embed-me/knx-kmp-watermeter/firmware/src/drivers/IDriverFactory.hpp

#ifndef _I_DRIVER_FACTORY_HPP_
#define _I_DRIVER_FACTORY_HPP_

#include "ITimerDriverFactory.hpp"
#include "IGpioDriverFactory.hpp"
#include "IKnxDriverFactory.hpp"
#include "IMotionDriverFactory.hpp"
#include "IWatermeterWakeupDriverFactory.hpp"
#include "rtc/IRtcDriver.hpp"
#include "logger/ILogger.hpp"
#include "watchdog/IWatchdogDriver.hpp"
#include "uart/IUartDriver.hpp"

namespace drivers {

class IDriverFactory : public IGpioDriverFactory,
                       public IKnxDriverFactory,
                       public IMotionDriverFactory,
                       public IWatermeterWakeupDriverFactory
{
public:
    ~IDriverFactory() = default;

    virtual std::shared_ptr<logger::ILogger> getLoggerDriver() = 0;
    virtual std::shared_ptr<watchdog::IWatchdogDriver> getWatchdogDriver() = 0;
    virtual std::shared_ptr<uart::IUartDriver> getUartDriver() = 0;
    virtual std::shared_ptr<timer::ITimerDriverFactory> getTimerDriverFactory() = 0;
    virtual std::shared_ptr<rtc::IRtcDriver> getRtcDriver() = 0;
};

}

#endif //_I_DRIVER_FACTORY_HPP_
