embed-me/knx-kmp-watermeter/firmware/src/application/WatermeterApp.cpp

#include "WatermeterApp.hpp"
#include "../drivers/logger/Logger.hpp"
#include "../utils/scheduler/Scheduler.hpp"
#include "../utils/knx/KnxDateTimeParser.hpp"
#include "../utils/knx/RtcSyncState.hpp"

using namespace drivers::logger;

constexpr uint32_t USEC_PER_SEC = 1000000;
constexpr uint32_t CRON_TICK_INTERVAL_US = 60 * USEC_PER_SEC;

namespace kmp = drivers::watermeter::kamstrup::transport;

namespace application {

WatermeterApp::WatermeterApp()
    : queueConfig_{}
{
}

void WatermeterApp::init(
    std::shared_ptr<drivers::uart::IUartDriver> uart,
    const drivers::uart::UartConfig& uartConfig,
    drivers::knx::KnxConfig& knxConfig,
    const kmp::CommandQueueConfig& queueConfig,
    std::shared_ptr<drivers::watermeter::wakeup::IWatermeterWakeupDriver> wakeupDriver,
    std::shared_ptr<drivers::timer::ITimerDriverFactory> timerFactory,
    std::shared_ptr<drivers::rtc::IRtcDriver> rtcDriver)
{
    knxConfig_ = &knxConfig;
    queueConfig_ = queueConfig;
    wakeupDriver_ = wakeupDriver;
    rtcDriver_ = rtcDriver;
    kmpUart_ = uart;
    if (!kmpUart_) {
        logWarning("KMP UART driver not available");
        return;
    }

    if (!kmpUart_->init(uartConfig)) {
        logError("KMP UART initialization failed");
        return;
    }

    initTransport(kmpUart_);
    if (kmpApplication_) {
        initRegisterCommands();
        initQueue(timerFactory);
        initTimers(timerFactory);
        initRtcCron();
    }
}

void WatermeterApp::process()
{
    if (kmpUart_) {
        kmpUart_->process();
    }
}

void WatermeterApp::initTransport(std::shared_ptr<drivers::uart::IUartDriver> uart)
{
    uint8_t addr = knxConfig_->getWatermeterConfig().destinationAddress;
    kmpPhysical_ = std::make_shared<kmp::PhysicalLayer>(uart);
    kmpDataLink_ = std::make_shared<kmp::DataLinkLayer>(kmpPhysical_, addr);
    kmpApplication_ = std::make_shared<kmp::ApplicationLayer>(kmpDataLink_);
    logInfo("KMP transport stack initialized");
}

void WatermeterApp::initRegisterCommands()
{
    auto regCfgs = knxConfig_->getWatermeterRegisterConfigs();
    auto linked = knxConfig_->getLinkedState();

    for (auto& reg : regCfgs) {
        if (!reg.enabled) {
            continue;
        }

        auto cmd = std::make_shared<kmp::GetRegisterCommand>(kmpApplication_, reg.registerId);
        cmd->registerListener([name = reg.name, go = reg.groupObject, dpt = reg.dpt,
                               linkGo = linked.groupObject, linkDpt = linked.dpt](const kmp::CommandResult& res){
            bool isOk = res.result == kmp::CommandResult::Result::OK;
            if (linkGo) {
                linkGo->valueCompare(KNXValue(isOk), linkDpt);
            }
            if (go && isOk) {
                go->value(KNXValue(res.value), dpt);
                logInfo("%s: %g %s", name, res.value,
                        kmp::unitToString(res.unit).c_str());
            } else {
                logWarning("Failed to get %s: with error %d", name, res.result);
            }
        });
        registerCmds_.push_back(cmd);
    }
}

void WatermeterApp::initQueue(std::shared_ptr<drivers::timer::ITimerDriverFactory> timerFactory)
{
    commandQueue_ = std::make_shared<kmp::CommandQueue>(
        kmpApplication_, queueConfig_, timerFactory);

    commandQueue_->setOnEmpty([this]() {
        onQueueEmpty();
    });
}

void WatermeterApp::initTimers(std::shared_ptr<drivers::timer::ITimerDriverFactory> timerFactory)
{
    cronTickTimer_ = timerFactory->getTimer();
    cronTickTimer_->setupInterruptHandler([](void* arg){
        auto* self = static_cast<WatermeterApp*>(arg);
        utils::Scheduler::schedule([self](void*) {
            self->onCronTick();
        });
    }, this);

    cronTickTimer_->start(CRON_TICK_INTERVAL_US, drivers::timer::TimerMode::RECURRING);
}

void WatermeterApp::initRtcCron()
{
    auto& timeGo = knxConfig_->getTimeGroupObject();
    timeGo.callback([this](GroupObject& go) {
        auto t = utils::knx::parseKnxTime(go.valueRef(), go.valueSize());
        if (!t.valid) {
            logWarning("Invalid KNX time telegram ignored");
            return;
        }

        if (rtcSync_.updateTime(t) && rtcDriver_) {
            const auto& dt = rtcSync_.dateTime();
            rtcDriver_->setDateTime(dt);
            logInfo("RTC updated from KNX: %04d-%02d-%02d %02d:%02d:%02d",
                    dt.year, dt.month, dt.day,
                    dt.hour, dt.minute, dt.second);
        }
    });

    auto& dateGo = knxConfig_->getDateGroupObject();
    dateGo.callback([this](GroupObject& go) {
        auto d = utils::knx::parseKnxDate(go.valueRef(), go.valueSize());
        if (!d.valid) {
            logWarning("Invalid KNX date telegram ignored");
            return;
        }

        if (rtcSync_.updateDate(d) && rtcDriver_) {
            const auto& dt = rtcSync_.dateTime();
            rtcDriver_->setDateTime(dt);
            logInfo("RTC updated from KNX: %04d-%02d-%02d %02d:%02d:%02d",
                    dt.year, dt.month, dt.day,
                    dt.hour, dt.minute, dt.second);
        }
    });

    updateCronMatcher();
}

void WatermeterApp::enqueuePendingCommands()
{
    if (commandQueue_) {
        for (auto& cmd : registerCmds_) {
            if (cmd) {
                commandQueue_->enqueue(cmd);
            }
        }
    }
}

void WatermeterApp::onQueueEmpty()
{
    wakeupDriver_->sleep();
}

void WatermeterApp::onCronTick()
{
    updateCronMatcher();

    if (!cronMatcher_ || !rtcDriver_) {
        return;
    }

    auto now = rtcDriver_->getDateTime();

    if (cronMatcher_->matches(now)) {
        int currentMinute = now.hour * 60 + now.minute;
        if (currentMinute != lastPollMinute_) {
            lastPollMinute_ = currentMinute;
            triggerDataRead();
        }
    }
}

void WatermeterApp::updateCronMatcher()
{
    if (!knxConfig_) return;

    auto cronExpr = knxConfig_->getPollingCronExpression();
    if (cronExpr == lastCronExpression_) {
        return;
    }

    lastCronExpression_ = cronExpr;
    if (cronExpr.empty()) {
        cronMatcher_.reset();
        logWarning("Cron expression is empty, data polling disabled");
        return;
    }

    cronMatcher_ = std::make_unique<utils::cron::CronMatcher>(cronExpr);
    logInfo("Cron expression updated: %s", cronExpr.c_str());
}

void WatermeterApp::triggerDataRead()
{
    wakeupDriver_->wakeup([this]() {
        enqueuePendingCommands();
    });
}

} // namespace application
