embed-me/knx-kmp-watermeter/firmware/src/application/WatermeterApp.hpp

#ifndef _WATERMETER_APP_HPP_
#define _WATERMETER_APP_HPP_

#include "IApplication.hpp"
#include "../drivers/watermeter/kamstrup/transport/layers/physical/PhysicalLayer.hpp"
#include "../drivers/watermeter/kamstrup/transport/layers/data_link/DataLinkLayer.hpp"
#include "../drivers/watermeter/kamstrup/transport/layers/application/ApplicationLayer.hpp"
#include "../drivers/watermeter/kamstrup/commands/GetRegisterCommand.hpp"
#include "../drivers/watermeter/kamstrup/utils/CommandQueue.hpp"
#include "../drivers/watermeter/wakeup/IWatermeterWakeupDriver.hpp"

#include "../drivers/rtc/IRtcDriver.hpp"
#include "../drivers/timer/ArduinoTimerFactory.hpp"
#include "../drivers/timer/ITimer.hpp"
#include "../utils/cron/CronMatcher.hpp"
#include "../utils/knx/RtcSyncState.hpp"

#include <memory>
#include <cstdint>
#include <vector>
#include <string>

namespace application {

class WatermeterApp : public IApplication {
public:
    WatermeterApp();
    ~WatermeterApp() override = default;

    void init(
        std::shared_ptr<drivers::uart::IUartDriver> uart,
        const drivers::uart::UartConfig& uartConfig,
        drivers::knx::KnxConfig& knxConfig,
        const drivers::watermeter::kamstrup::transport::CommandQueueConfig& queueConfig,
        std::shared_ptr<drivers::watermeter::wakeup::IWatermeterWakeupDriver> wakeupDriver,
        std::shared_ptr<drivers::timer::ITimerDriverFactory> timerFactory,
        std::shared_ptr<drivers::rtc::IRtcDriver> rtcDriver
    );
    void process() override;

private:
    void initTransport(std::shared_ptr<drivers::uart::IUartDriver> uart);
    void initRegisterCommands();
    void initQueue(std::shared_ptr<drivers::timer::ITimerDriverFactory> timerFactory);
    void initTimers(std::shared_ptr<drivers::timer::ITimerDriverFactory> timerFactory);
    void initRtcCron();
    void enqueuePendingCommands();
    void onQueueEmpty();

    void onCronTick();
    void updateCronMatcher();
    void triggerDataRead();

    std::shared_ptr<drivers::watermeter::kamstrup::transport::IPhysicalLayer> kmpPhysical_;
    std::shared_ptr<drivers::watermeter::kamstrup::transport::IDataLinkLayer> kmpDataLink_;
    std::shared_ptr<drivers::watermeter::kamstrup::transport::IApplicationLayer> kmpApplication_;

    std::vector<std::shared_ptr<drivers::watermeter::kamstrup::transport::GetRegisterCommand>> registerCmds_;

    std::shared_ptr<drivers::watermeter::kamstrup::transport::CommandQueue> commandQueue_;
    std::shared_ptr<drivers::timer::ITimer> cronTickTimer_;

    std::shared_ptr<drivers::uart::IUartDriver> kmpUart_;
    drivers::knx::KnxConfig* knxConfig_ = nullptr;
    drivers::watermeter::kamstrup::transport::CommandQueueConfig queueConfig_;

    std::shared_ptr<drivers::watermeter::wakeup::IWatermeterWakeupDriver> wakeupDriver_;

    std::shared_ptr<drivers::rtc::IRtcDriver> rtcDriver_;
    std::unique_ptr<utils::cron::CronMatcher> cronMatcher_;
    std::string lastCronExpression_;
    int lastPollMinute_ = -1;
    utils::knx::RtcSyncState rtcSync_;
};

}

#endif // _WATERMETER_APP_HPP_
