embed-me/knx-kmp-watermeter/firmware/src/application/IApplication.hpp

#ifndef _I_APPLICATION_HPP_
#define _I_APPLICATION_HPP_

#include "../drivers/uart/IUartDriver.hpp"
#include "../drivers/timer/ArduinoTimerFactory.hpp"
#include "../drivers/knx/data/KnxConfig.hpp"
#include "../drivers/rtc/IRtcDriver.hpp"
#include "../drivers/watermeter/kamstrup/utils/CommandQueueConfig.hpp"
#include "../drivers/watermeter/wakeup/IWatermeterWakeupDriver.hpp"

#include <memory>

namespace application {

class IApplication {
public:
    virtual ~IApplication() = default;

    virtual void process() = 0;
};

}

#endif // _I_APPLICATION_HPP_
